makersmakingchange/Oak-Compact-Joystick/Documentation/Working_Documents/Assets/Joystick_Alignment_Line.jpg

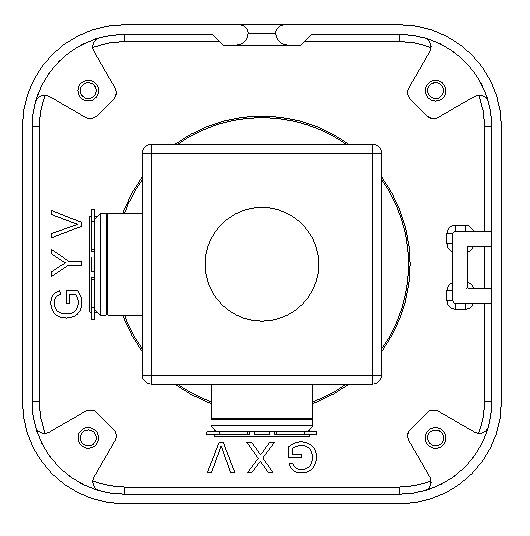
Documentation/Working_Documents/Assets/Joystick_Alignment_Line.jpg
