makersmakingchange/Oak-Compact-Joystick/Documentation/Working_Documents/Assets/Joystick_Line.jpg

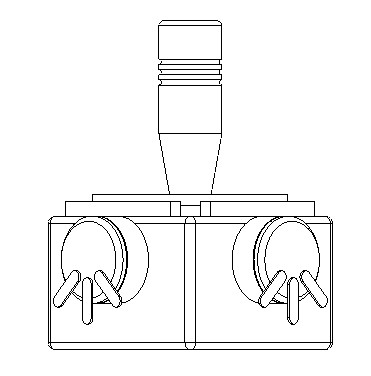
Documentation/Working_Documents/Assets/Joystick_Line.jpg
