makersmakingchange/Oak-Compact-Joystick/Documentation/Working_Documents/Assets/Multimeter_Video_QR.png

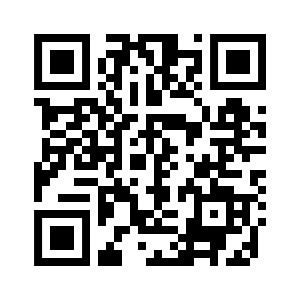
Documentation/Working_Documents/Assets/Multimeter_Video_QR.png
