makersmakingchange/Oak-Compact-Joystick/Documentation/Working_Documents/Assets/wires.png

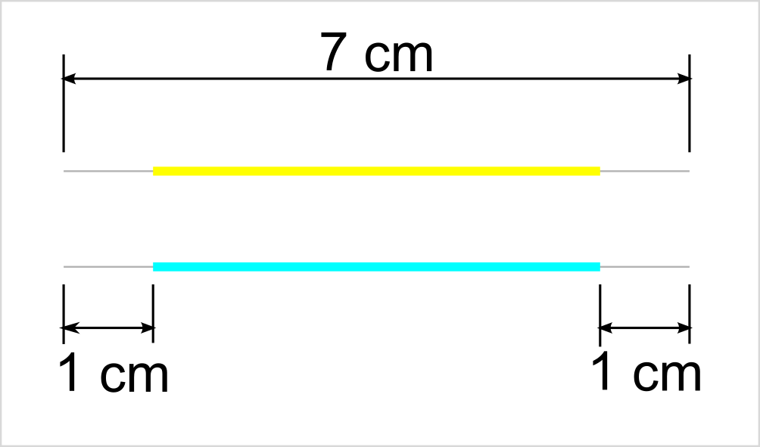
Documentation/Working_Documents/Assets/wires.png
