makersmakingchange/Oak-Compact-Joystick/Documentation/Working_Documents/Assets/Component_Photos/M3_nuts.jpg

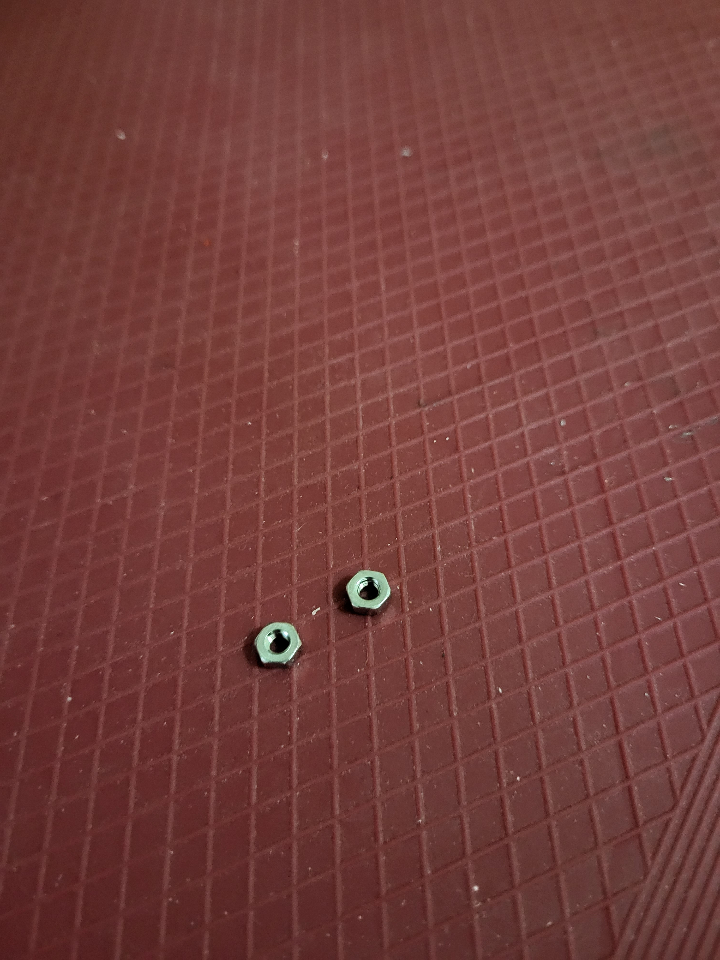
Documentation/Working_Documents/Assets/Component_Photos/M3_nuts.jpg
