makersmakingchange/Oak-Compact-Joystick/Documentation/Working_Documents/Assets/Component_Photos/T-nut.jpg

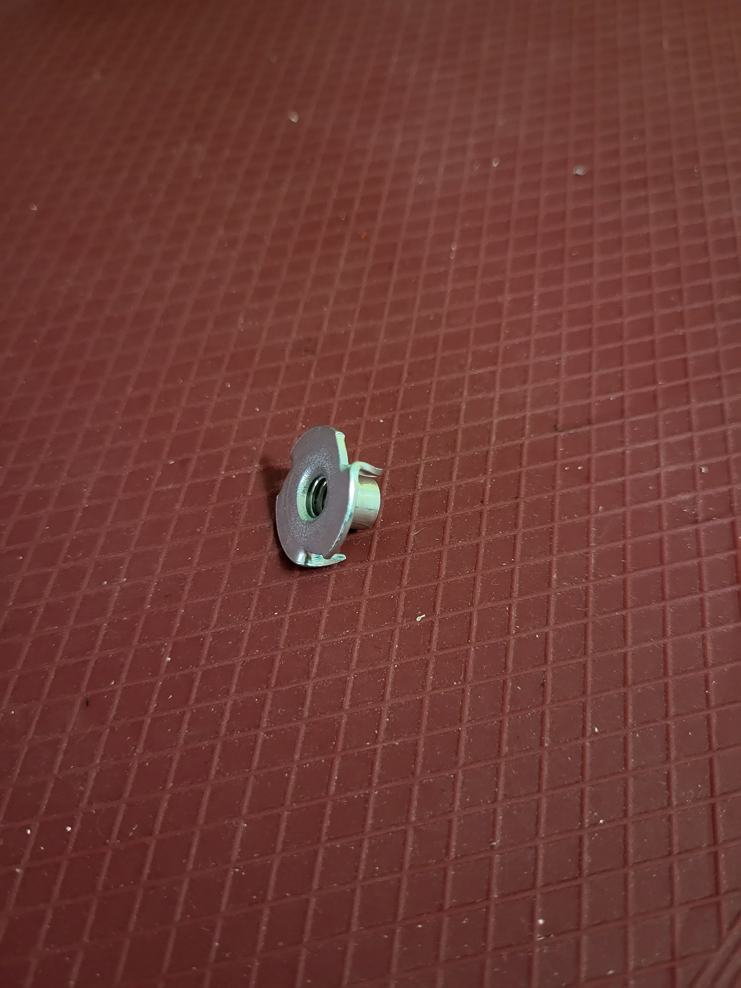
Documentation/Working_Documents/Assets/Component_Photos/T-nut.jpg
