makersmakingchange/Oak-Compact-Joystick/Build_Files/3D_Printing_Files/Oak_Enclosure_Bottom.stl

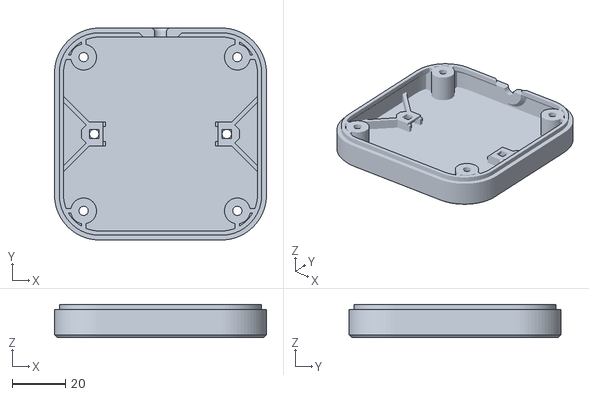
[picture p25: CAD file, 2023-09-29]
Build_Files/3D_Printing_Files/Oak_Enclosure_Bottom.stl
80.0 x 80.0 x 12.5
