makersmakingchange/Oak-Compact-Joystick/Build_Files/3D_Printing_Files/Toppers/Large/Large_Stick_Topper.stl

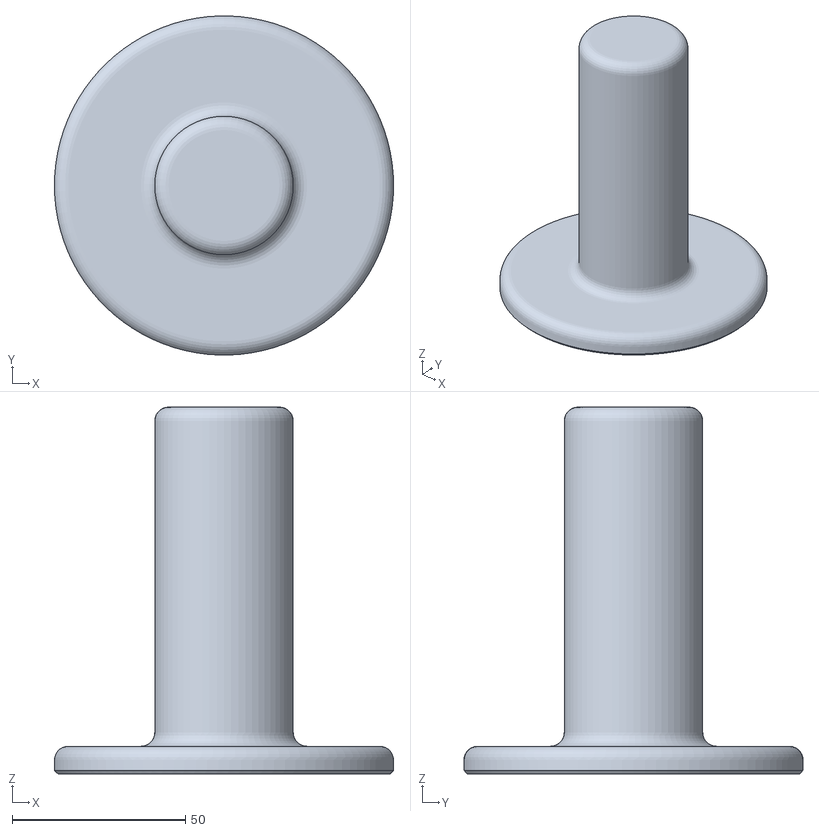
[picture p26: CAD file, 2023-09-29]
Build_Files/3D_Printing_Files/Toppers/Large/Large_Stick_Topper.stl
98.0 x 97.9 x 106.0
