makersmakingchange/Oak-Compact-Joystick/Build_Files/3D_Printing_Files/Toppers/Medium/Medium_Concave_Topper.stl

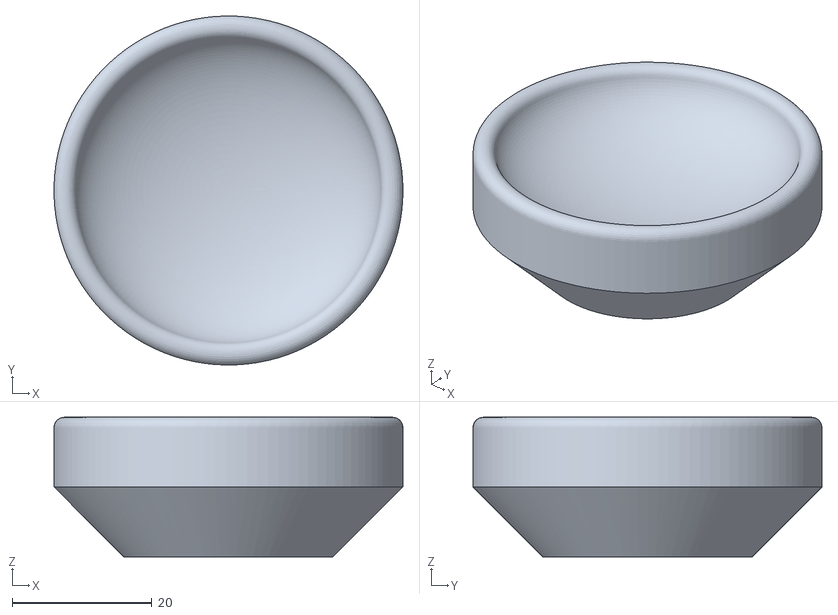
[picture p27: CAD file, 2023-09-29]
Build_Files/3D_Printing_Files/Toppers/Medium/Medium_Concave_Topper.stl
50.0 x 50.0 x 20.0
