makersmakingchange/Oak-Compact-Joystick/Build_Files/3D_Printing_Files/Toppers/Small/Small_Convex_Topper.stl

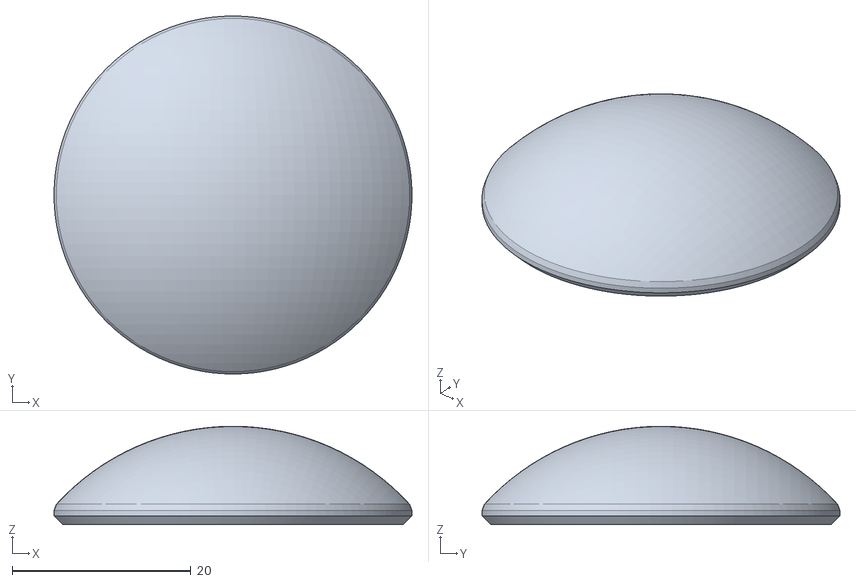
[picture p28: CAD file, 2023-09-29]
Build_Files/3D_Printing_Files/Toppers/Small/Small_Convex_Topper.stl
40.0 x 40.0 x 11.0
