makersmakingchange/Oak-Compact-Joystick/Build_Files/3D_Printing_Files/Toppers/Large/Large_Concave_Topper.stl

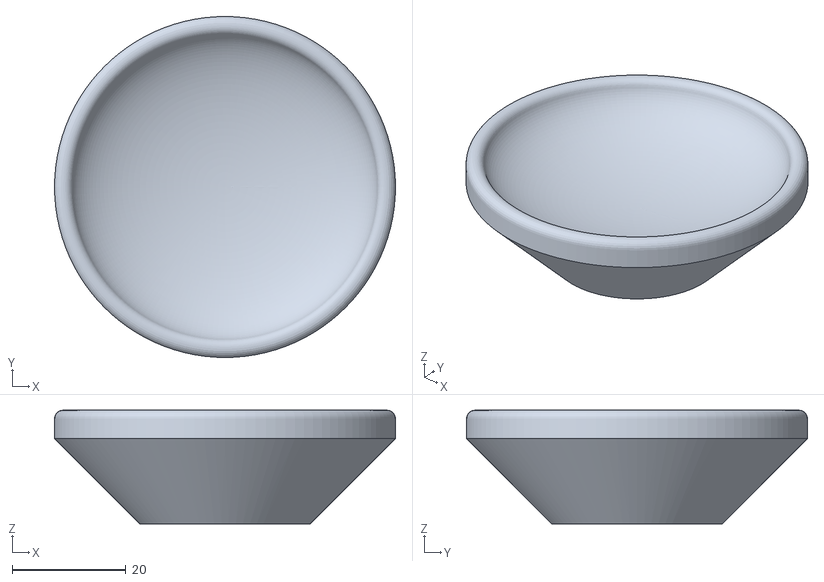
[picture p29: CAD file, 2023-09-29]
Build_Files/3D_Printing_Files/Toppers/Large/Large_Concave_Topper.stl
60.0 x 60.0 x 20.0
