makersmakingchange/Oak-Compact-Joystick/Build_Files/3D_Printing_Files/Toppers/Medium/Medium_Stick_Topper.stl

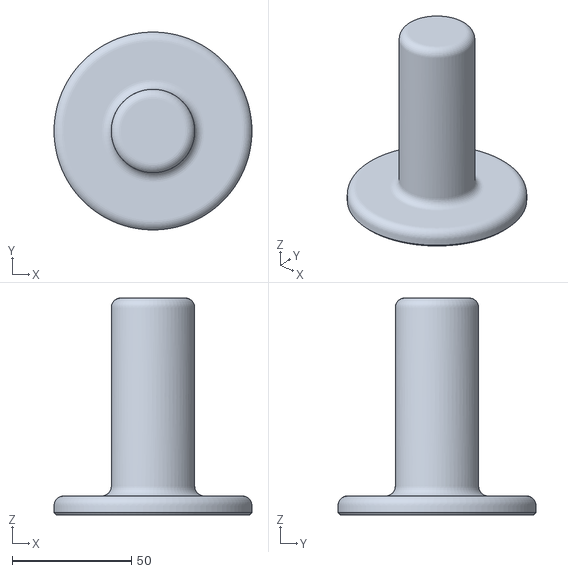
[picture p30: CAD file, 2023-09-29]
Build_Files/3D_Printing_Files/Toppers/Medium/Medium_Stick_Topper.stl
83.0 x 83.0 x 91.0
