makersmakingchange/Oak-Compact-Joystick/Build_Files/3D_Printing_Files/Toppers/Small/Small_Concave_Topper.stl

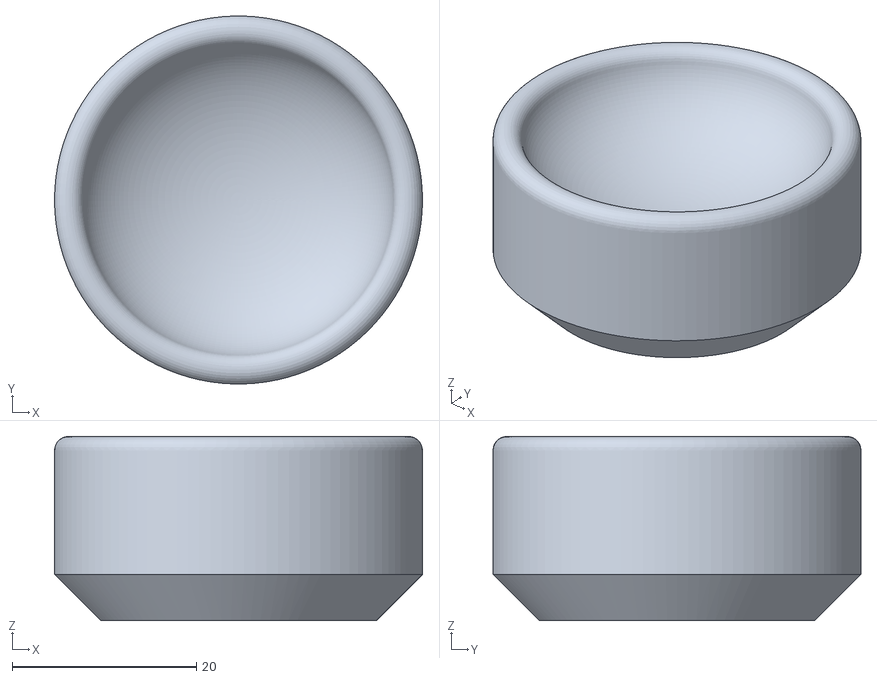
[picture p31: CAD file, 2023-09-29]
Build_Files/3D_Printing_Files/Toppers/Small/Small_Concave_Topper.stl
40.0 x 40.0 x 20.0
