makersmakingchange/Oak-Compact-Joystick/Documentation/Working_Documents/Assets/3D_Print_Photos/Oak_Enclosure_Top_2.jpg

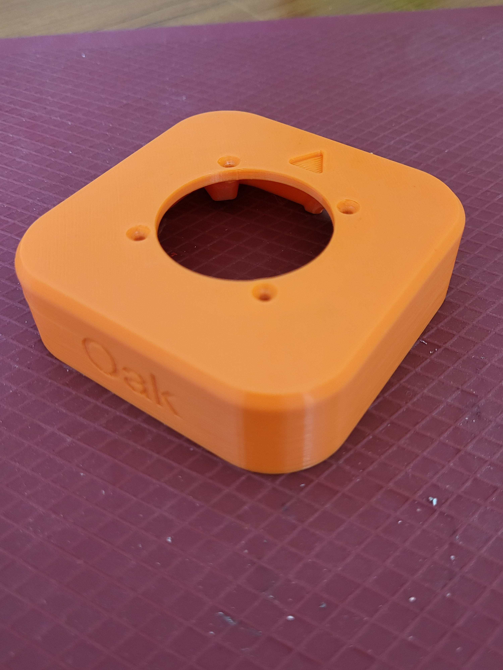
Documentation/Working_Documents/Assets/3D_Print_Photos/Oak_Enclosure_Top_2.jpg
