makersmakingchange/Oak-Compact-Joystick/Documentation/Working_Documents/Assets/3D_Print_Photos/Oak_Wrench_Crop.jpg

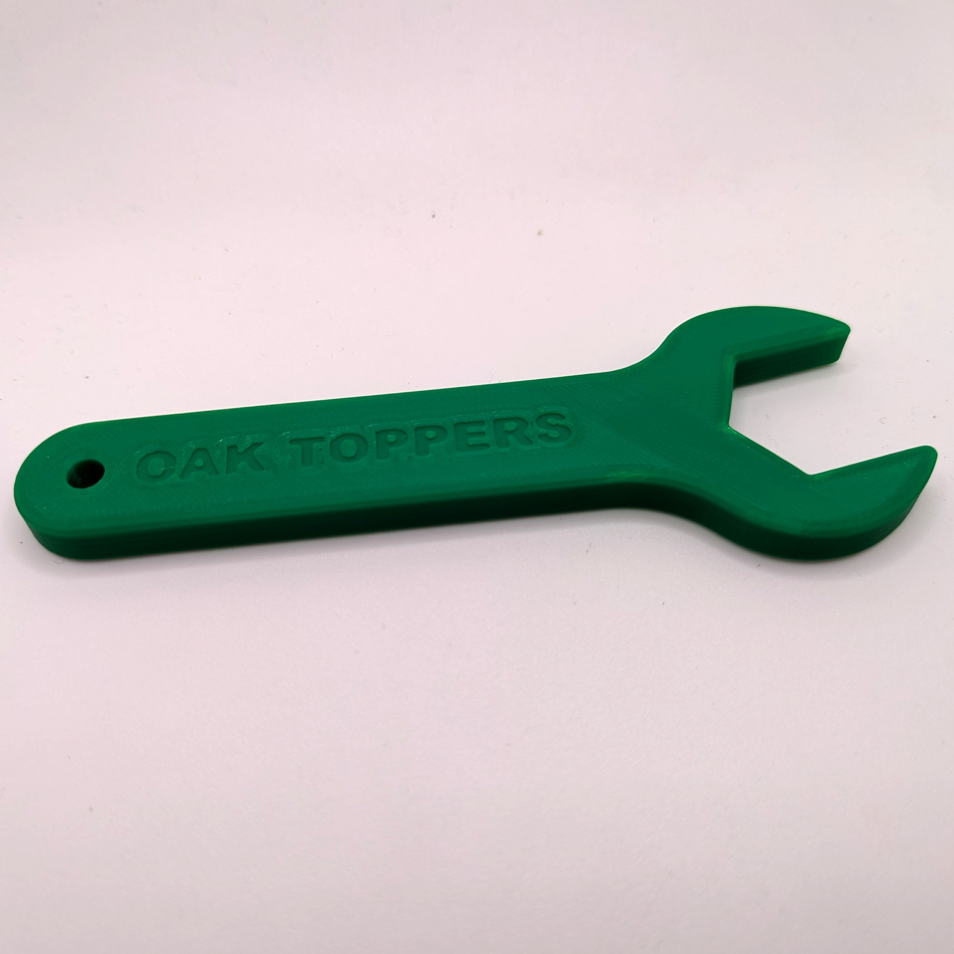
Documentation/Working_Documents/Assets/3D_Print_Photos/Oak_Wrench_Crop.jpg
