makersmakingchange/Oak-Compact-Joystick/Documentation/Working_Documents/Assets/Assembly_Photos/Oak_bottom.jpg

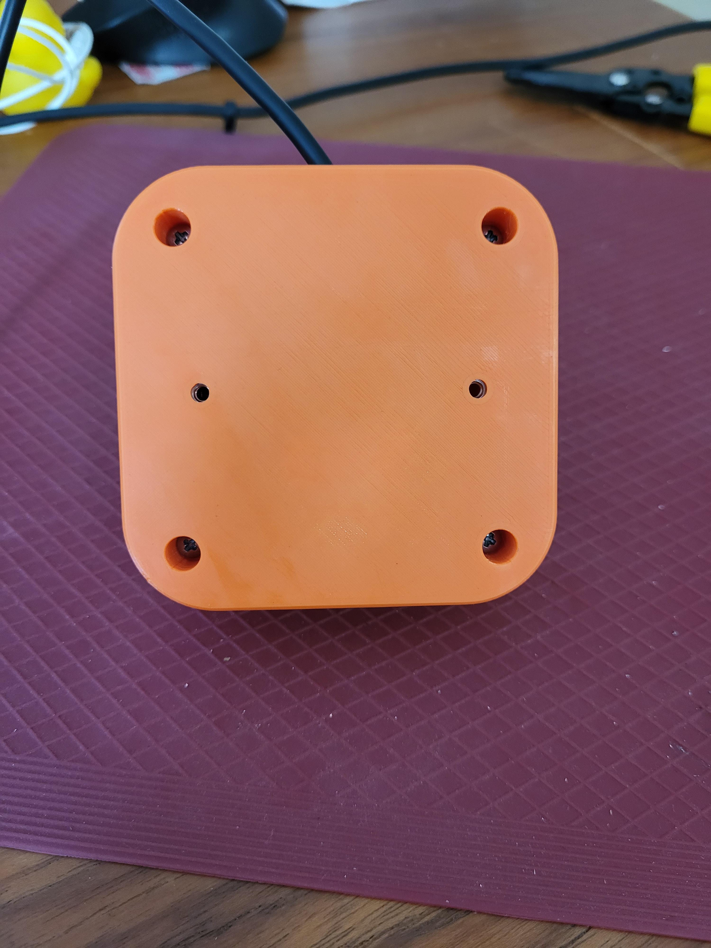
Documentation/Working_Documents/Assets/Assembly_Photos/Oak_bottom.jpg
