makersmakingchange/Oak-Compact-Joystick/Documentation/Working_Documents/Assets/Assembly_Photos/Oak_enclosure_assembly.jpg

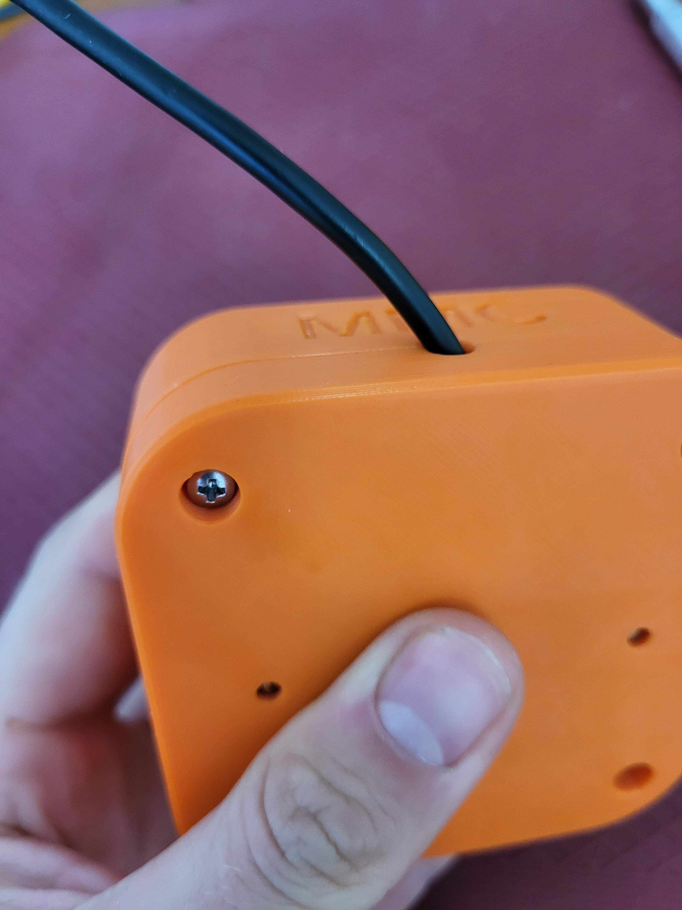
Documentation/Working_Documents/Assets/Assembly_Photos/Oak_enclosure_assembly.jpg
