makersmakingchange/Oak-Compact-Joystick/Documentation/Working_Documents/Assets/Assembly_Photos/Oak_fastening_joystick.jpg

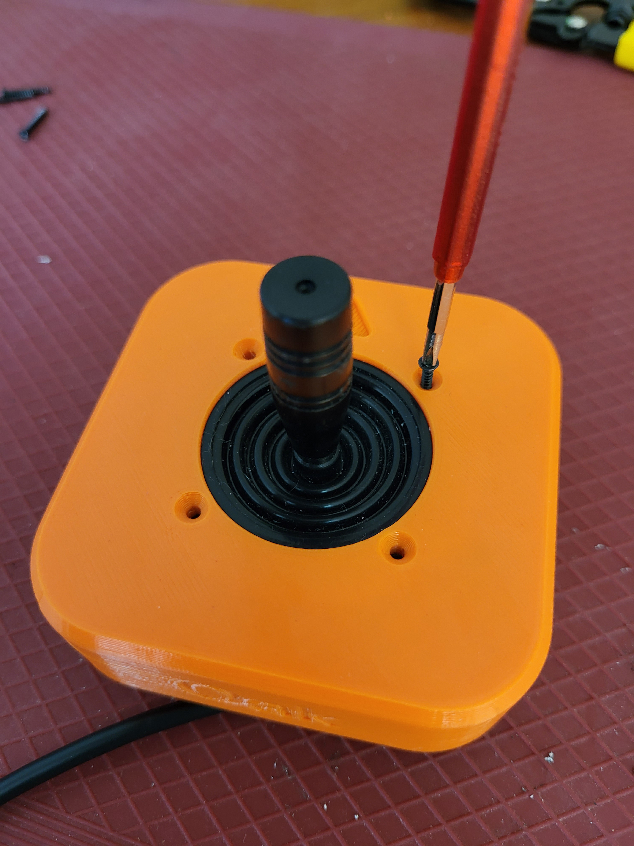
Documentation/Working_Documents/Assets/Assembly_Photos/Oak_fastening_joystick.jpg
