makersmakingchange/Oak-Compact-Joystick/Documentation/Working_Documents/Assets/Assembly_Photos/Oak_joystick_fastened.jpg

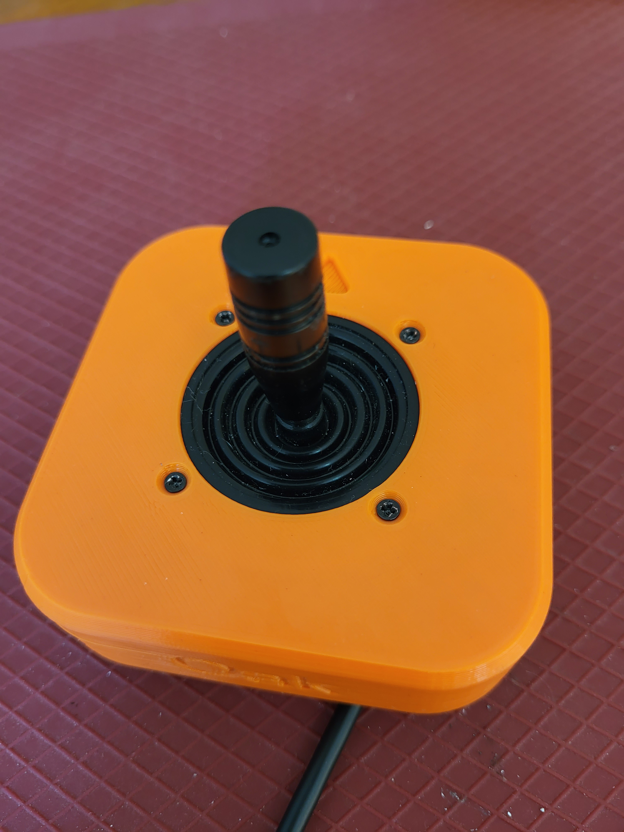
Documentation/Working_Documents/Assets/Assembly_Photos/Oak_joystick_fastened.jpg
