makersmakingchange/Oak-Compact-Joystick/Documentation/Working_Documents/Assets/Assembly_Photos/Oak_joystick_inserted.jpg

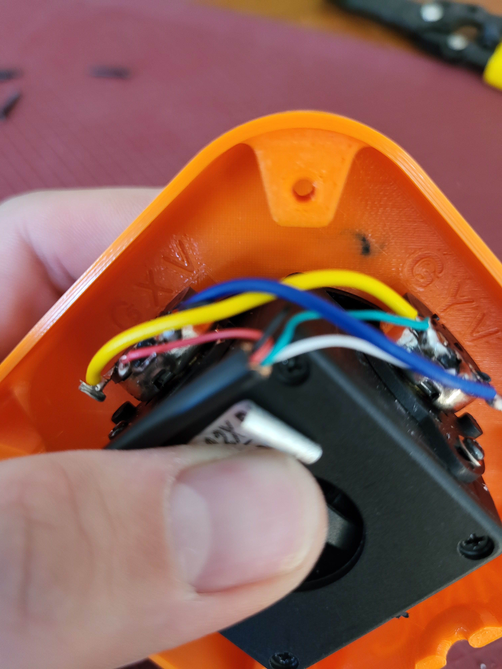
Documentation/Working_Documents/Assets/Assembly_Photos/Oak_joystick_inserted.jpg
