makersmakingchange/Oak-Compact-Joystick/Documentation/Working_Documents/Assets/Assembly_Photos/Oak_joystick_solder_4.jpg

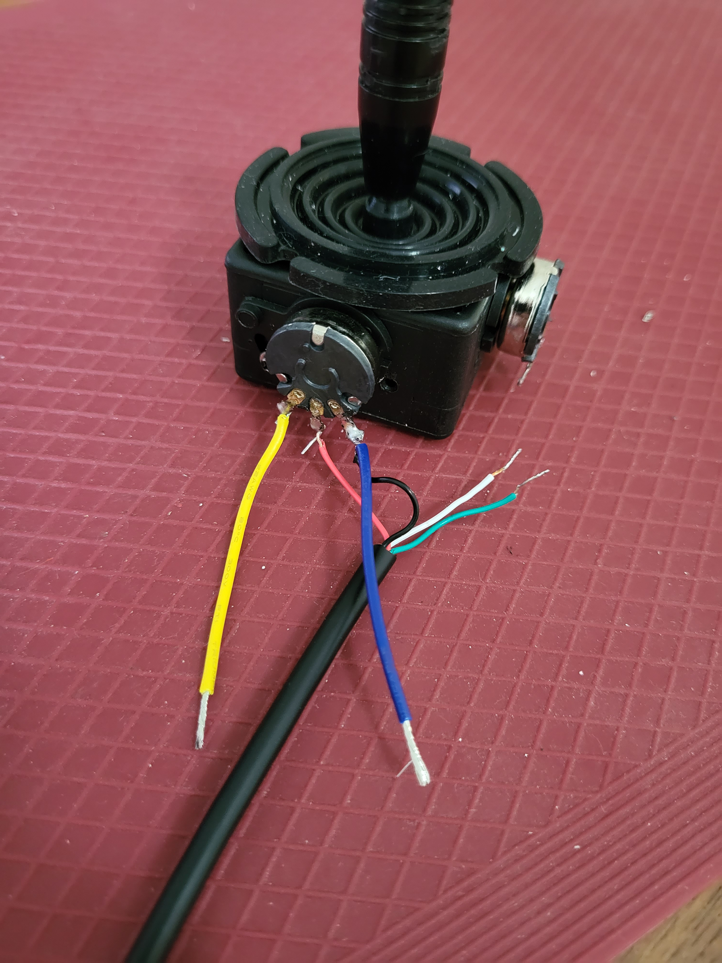
Documentation/Working_Documents/Assets/Assembly_Photos/Oak_joystick_solder_4.jpg
