makersmakingchange/Oak-Compact-Joystick/Documentation/Working_Documents/Assets/Assembly_Photos/Oak_joystick_solder_6.jpg

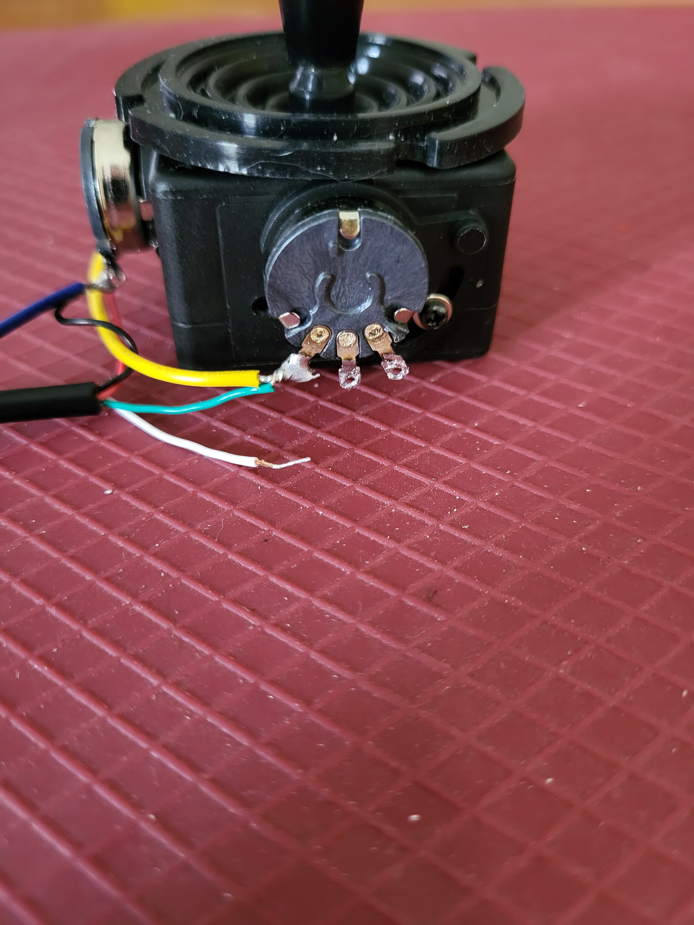
Documentation/Working_Documents/Assets/Assembly_Photos/Oak_joystick_solder_6.jpg
