makersmakingchange/Oak-Compact-Joystick/Documentation/Working_Documents/Assets/Assembly_Photos/Oak_wiring_Diagram.png

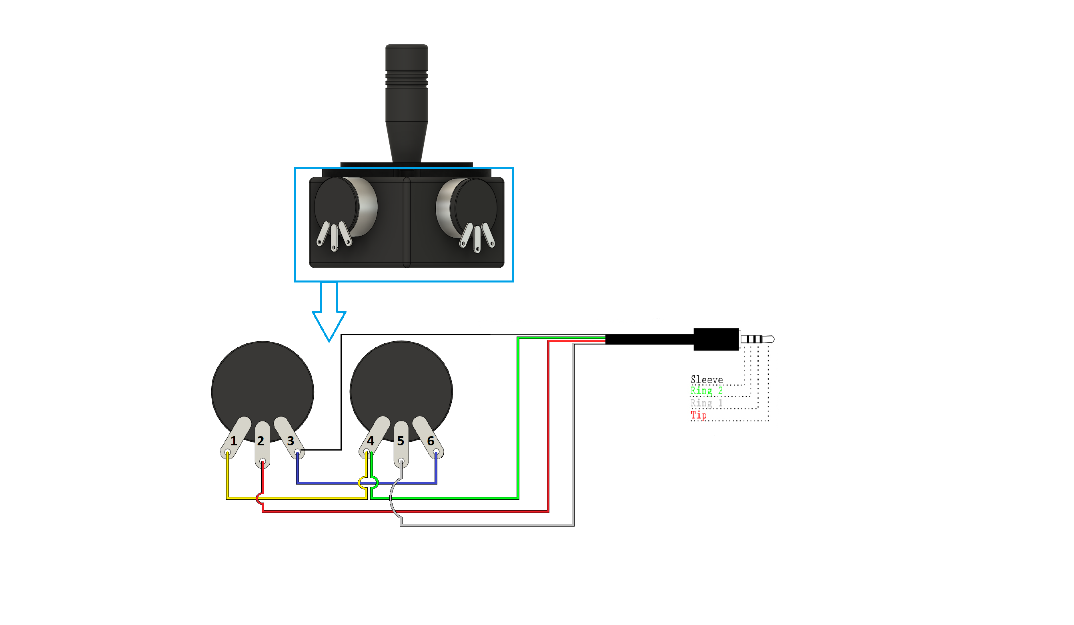
Documentation/Working_Documents/Assets/Assembly_Photos/Oak_wiring_Diagram.png
