makersmakingchange/Oak-Compact-Joystick/Documentation/Working_Documents/Assets/Assembly_Photos/Oak_zip_tie_anchor.jpg

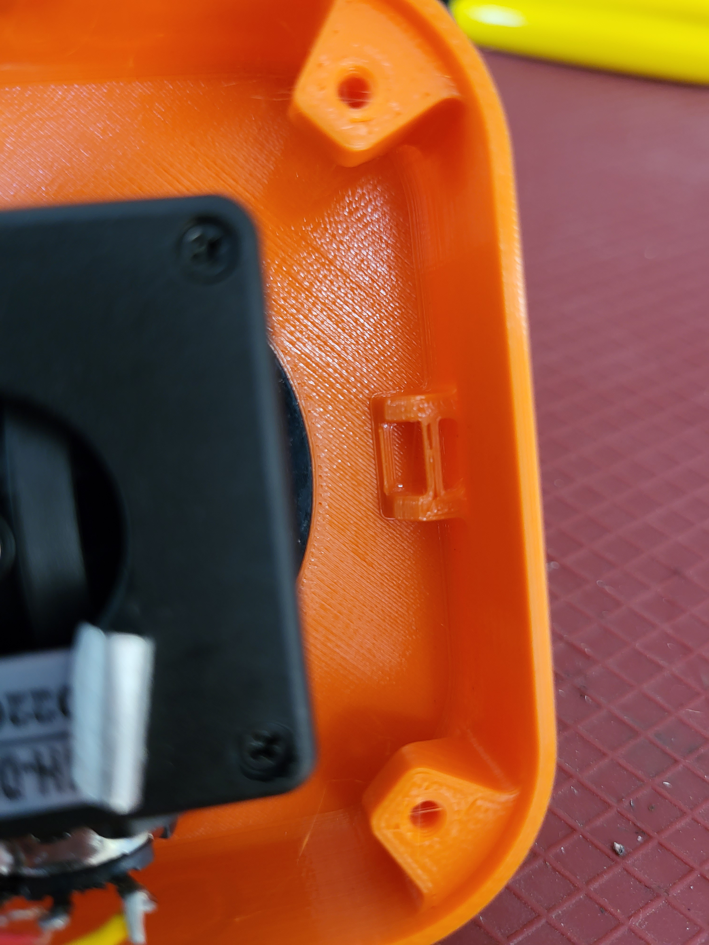
Documentation/Working_Documents/Assets/Assembly_Photos/Oak_zip_tie_anchor.jpg
