makersmakingchange/Oak-Compact-Joystick/Documentation/Working_Documents/Assets/Oak-Goalpost-Small.pdf

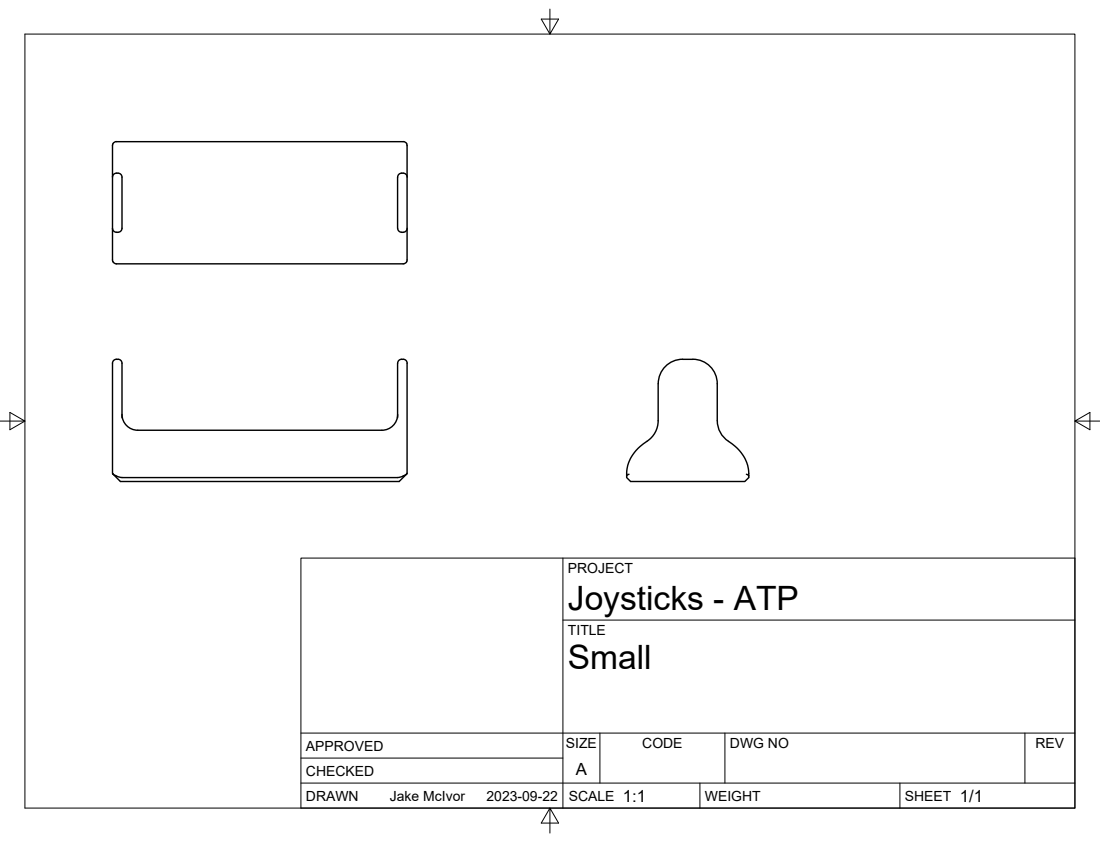
[picture p123: page 1]
SIZE; CODE; DWG NO; REV; Jake McIvor; Joysticks - ATP
