makersmakingchange/Oak-Compact-Joystick/Documentation/Working_Documents/Assets/Stick Toppers Drawing v1.pdf

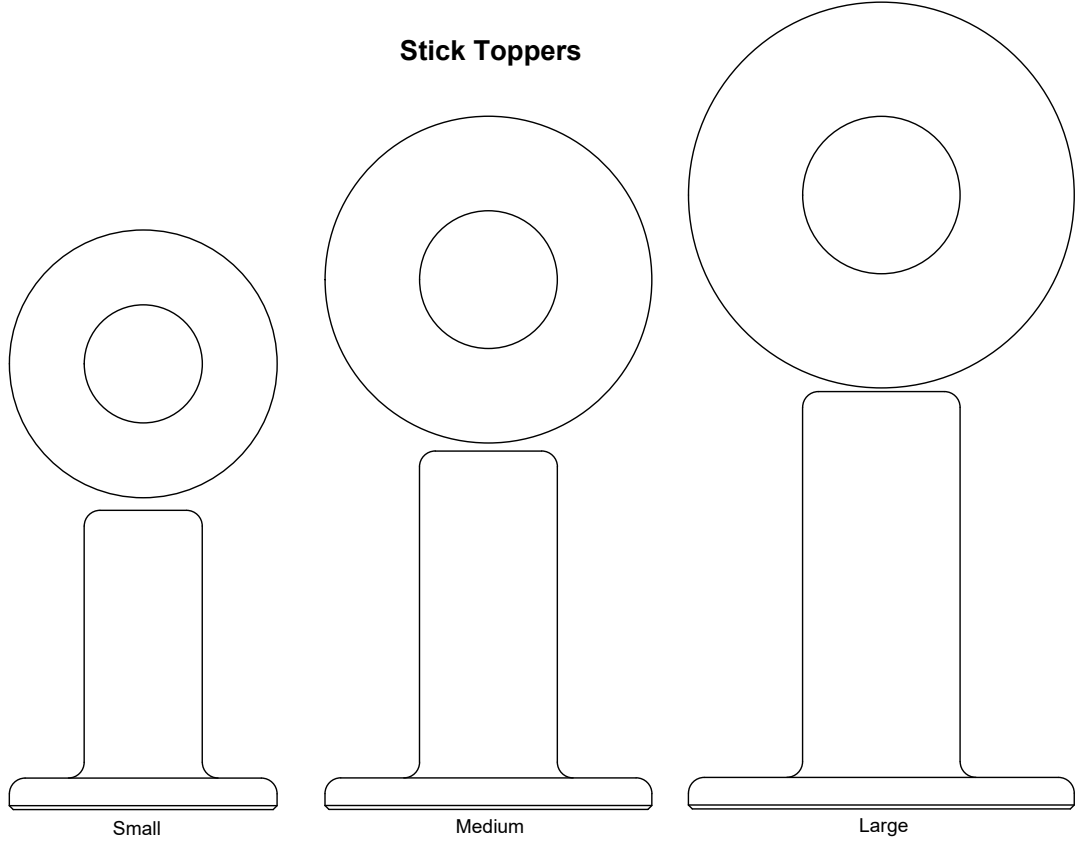
[picture p124: page 1]
Stick Toppers
