makersmakingchange/Oak-Compact-Joystick/Documentation/Working_Documents/Assets/Assembly_Photos/Oak_cable_routing.jpg

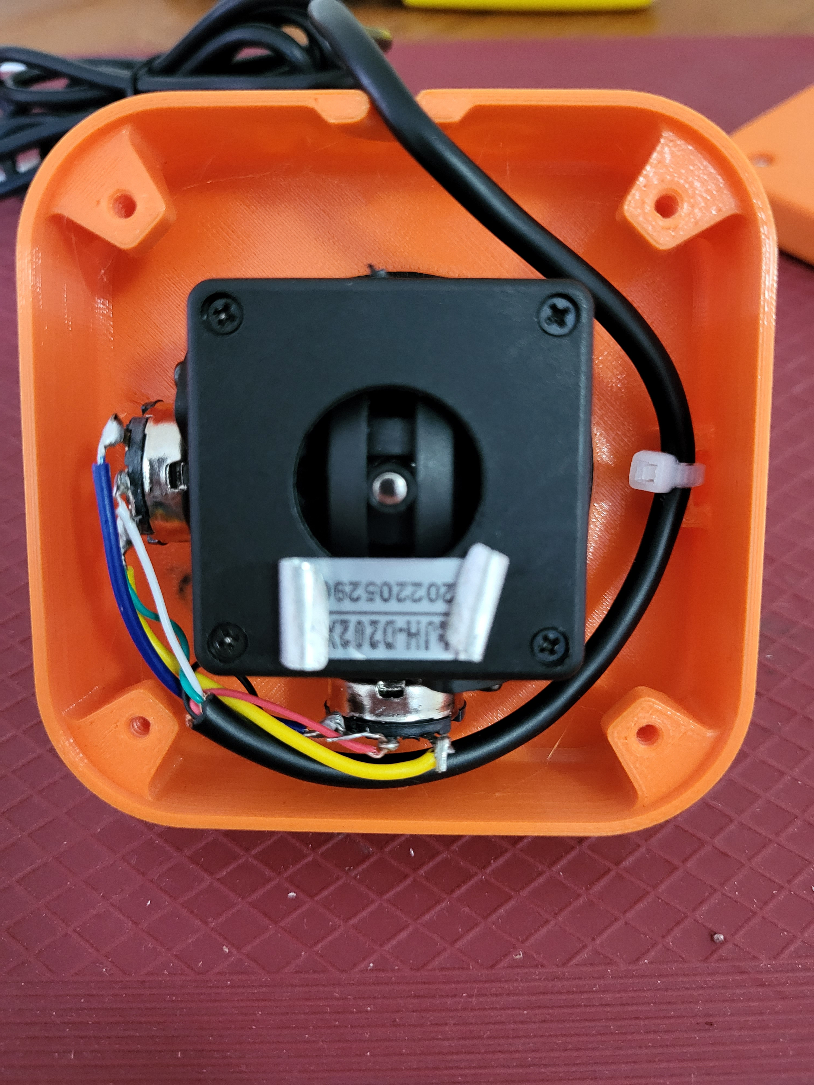
Documentation/Working_Documents/Assets/Assembly_Photos/Oak_cable_routing.jpg
