makersmakingchange/Oak-Compact-Joystick/Documentation/Working_Documents/Assets/Assembly_Photos/Oak_Joystick_Complete.jpg

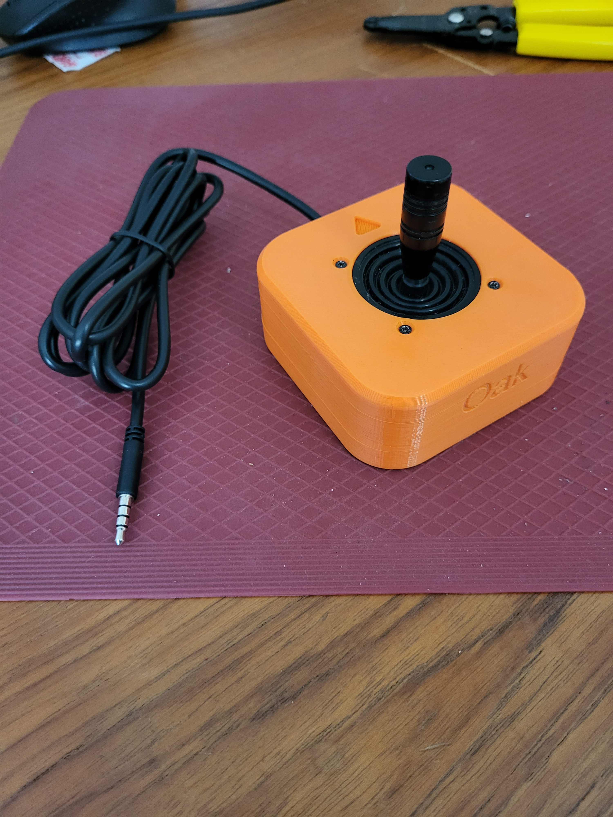
Documentation/Working_Documents/Assets/Assembly_Photos/Oak_Joystick_Complete.jpg
